YakshithK/K-Logic/Screenshots/Screenshot 2026-03-21 152913.png

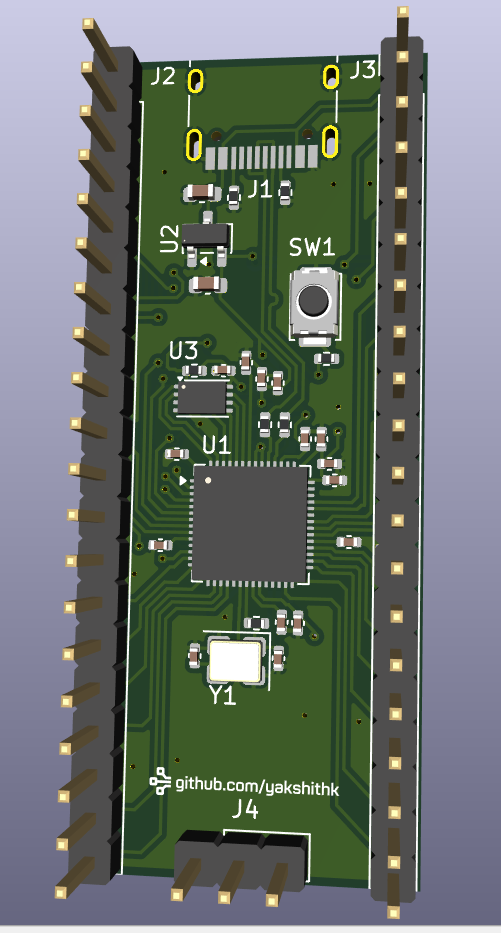
Screenshots/Screenshot 2026-03-21 152913.png
