YakshithK/K-Logic/Screenshots/Screenshot 2026-03-10 000626.png

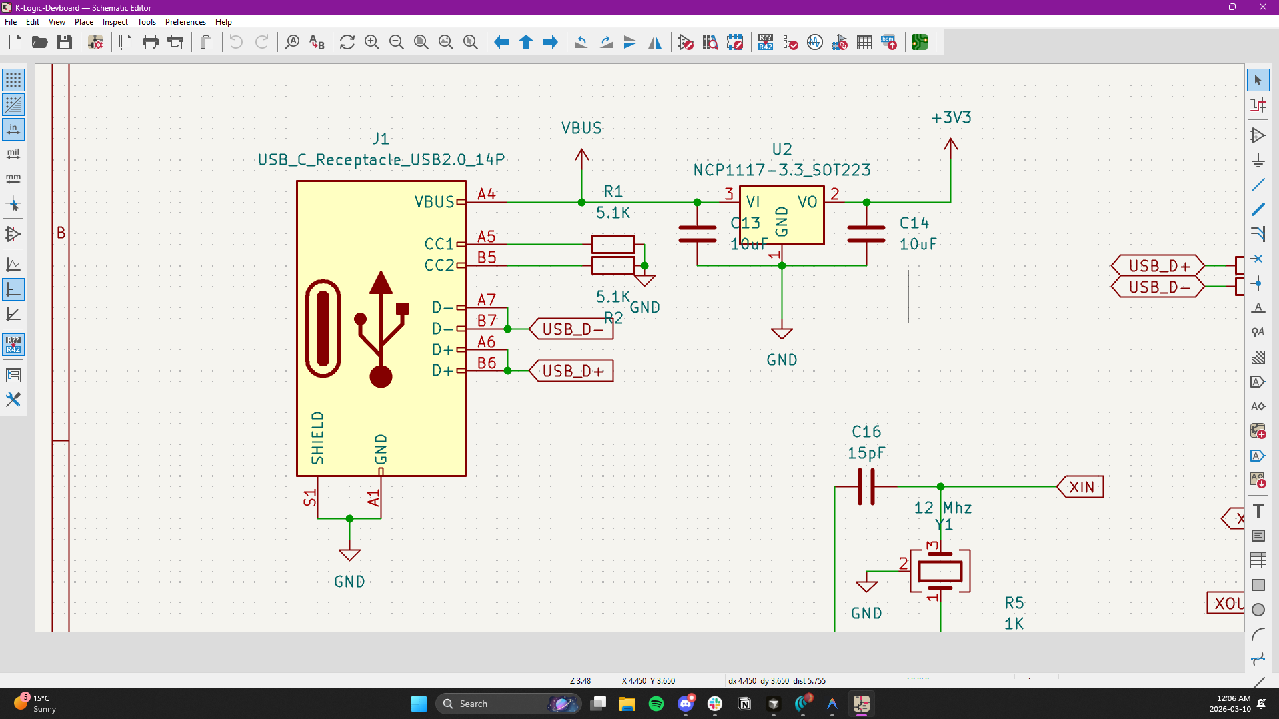
Screenshots/Screenshot 2026-03-10 000626.png
