YakshithK/K-Logic/Screenshots/Screenshot 2026-03-10 092232.png

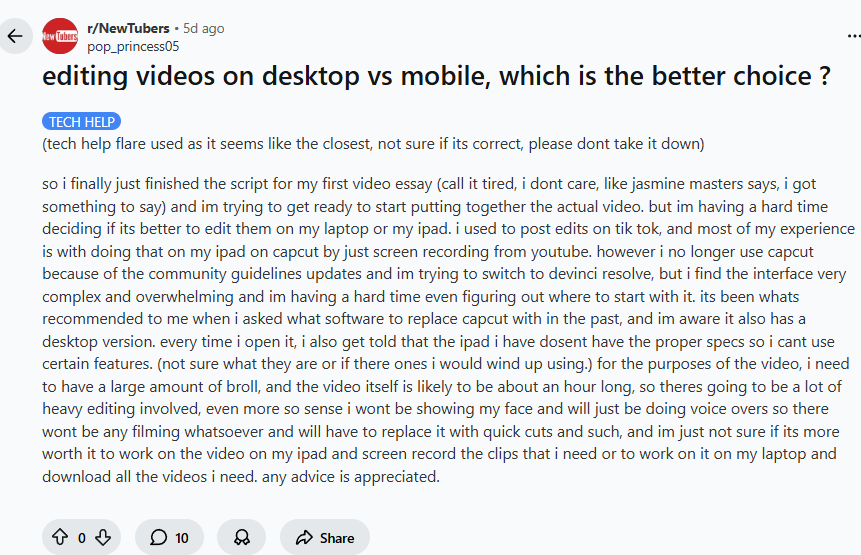
Screenshots/Screenshot 2026-03-10 092232.png
