YakshithK/K-Logic/Screenshots/Screenshot 2026-03-10 194304.png

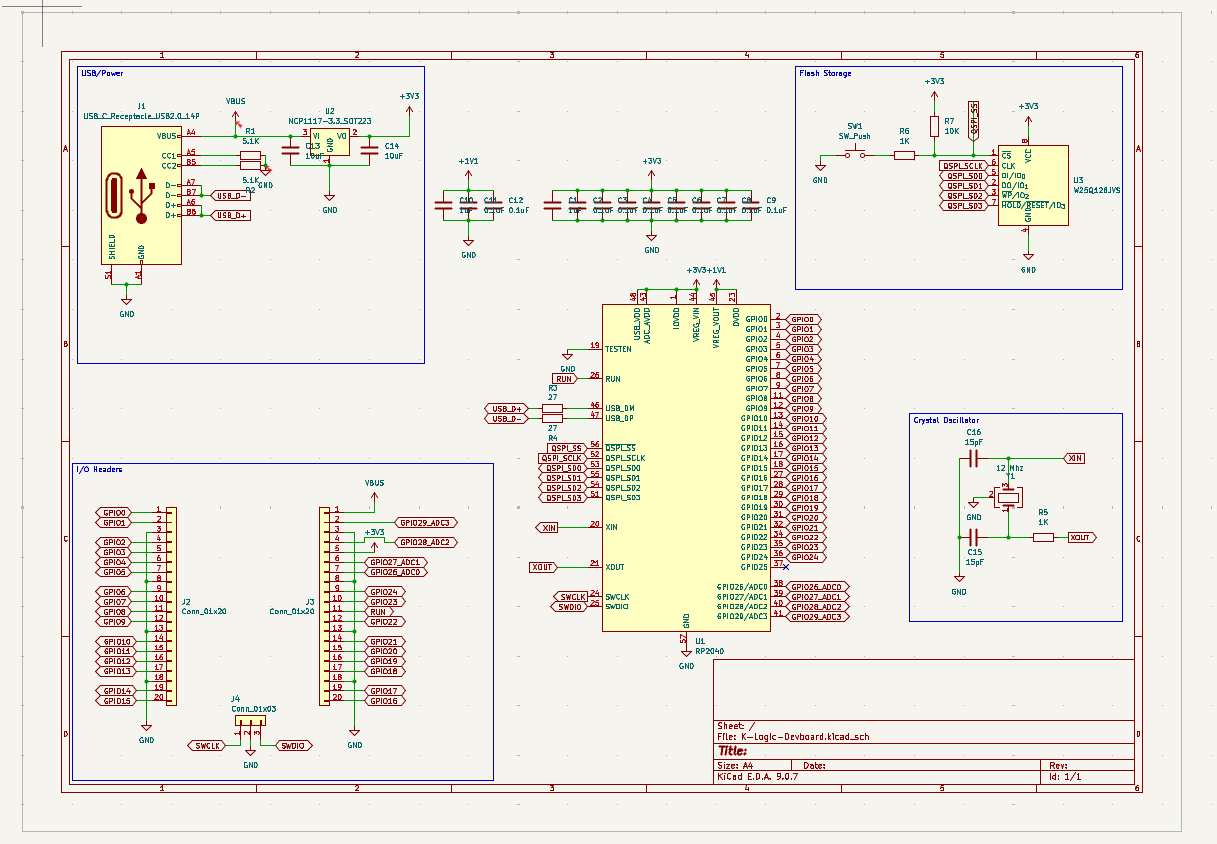
Screenshots/Screenshot 2026-03-10 194304.png
