YakshithK/K-Logic/Screenshots/Screenshot 2026-03-10 195755.png

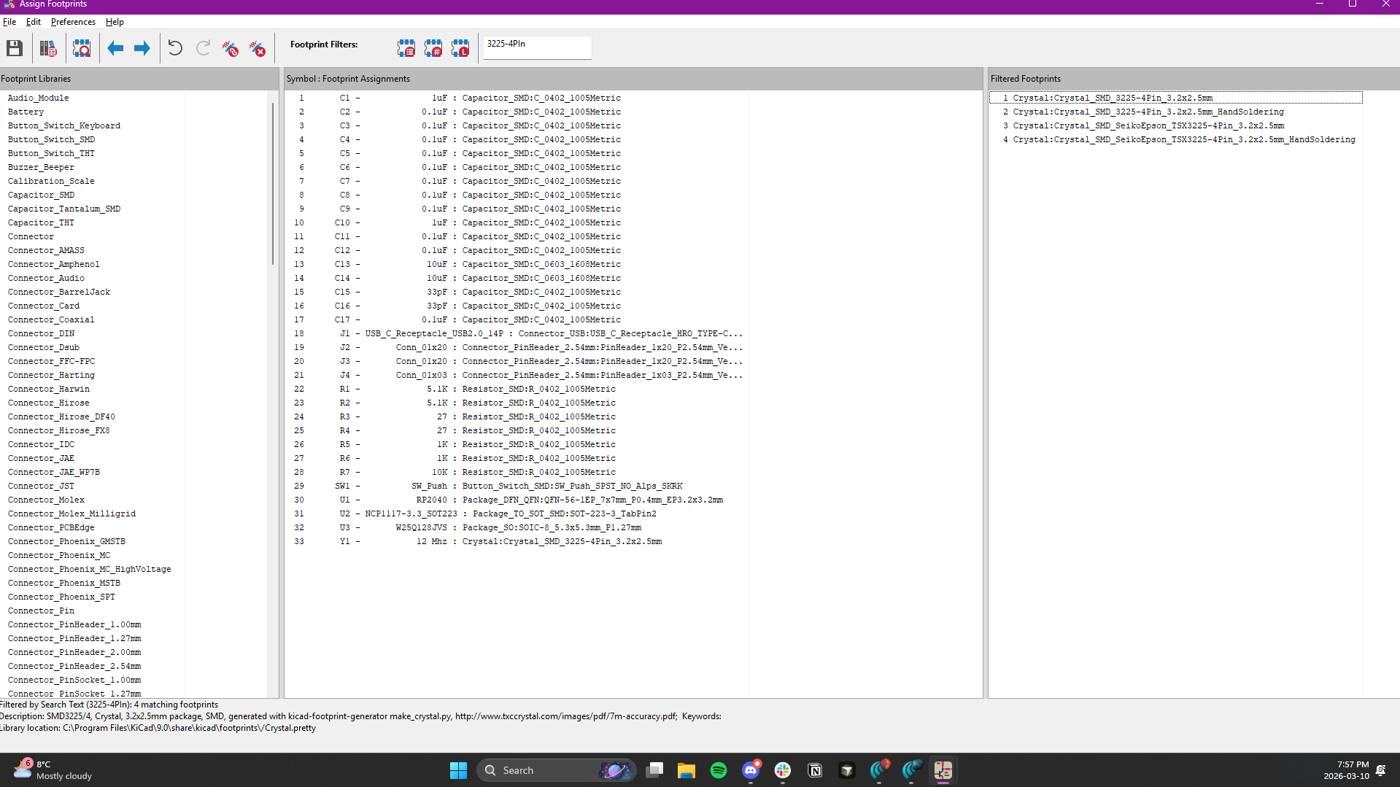
Screenshots/Screenshot 2026-03-10 195755.png
