YakshithK/K-Logic/Screenshots/Screenshot 2026-03-11 165531.png

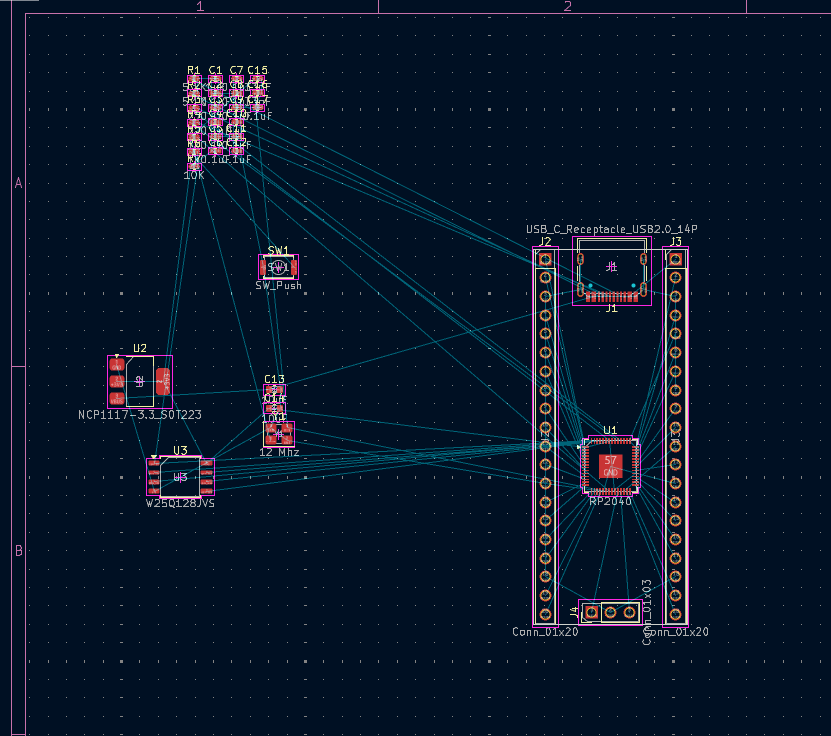
Screenshots/Screenshot 2026-03-11 165531.png
