YakshithK/K-Logic/Screenshots/Screenshot 2026-03-14 103205.png

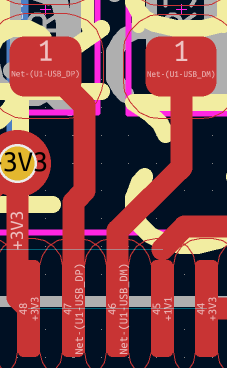
Screenshots/Screenshot 2026-03-14 103205.png
