YakshithK/K-Logic/Screenshots/Screenshot 2026-03-14 105847.png

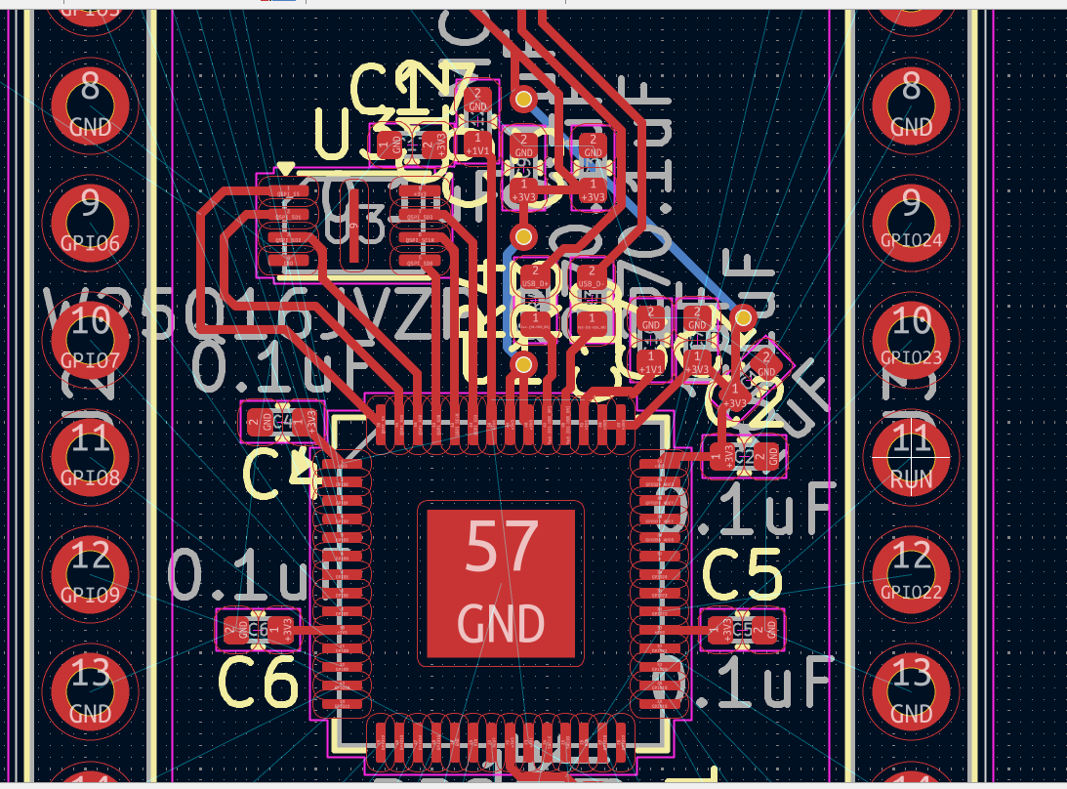
Screenshots/Screenshot 2026-03-14 105847.png
