YakshithK/K-Logic/Screenshots/Screenshot 2026-03-14 121532.png

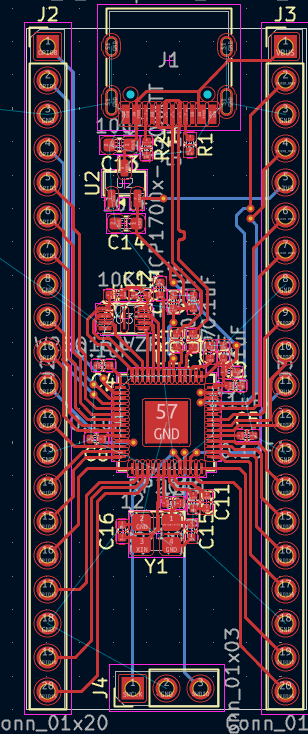
Screenshots/Screenshot 2026-03-14 121532.png
