YakshithK/K-Logic/Screenshots/Screenshot 2026-03-14 193433.png

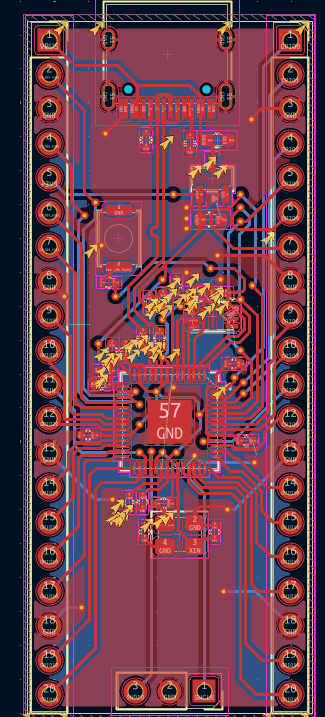
Screenshots/Screenshot 2026-03-14 193433.png
