YakshithK/K-Logic/Screenshots/Screenshot 2026-03-14 193438.png

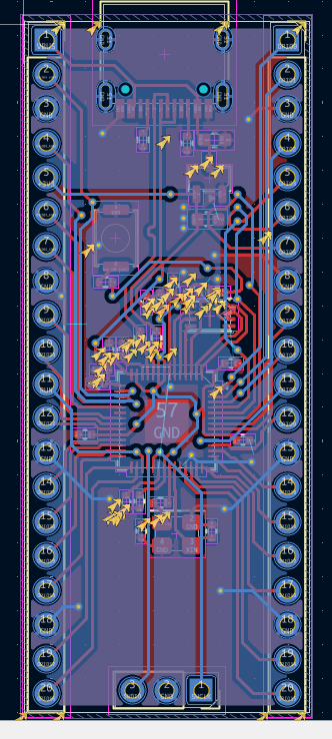
Screenshots/Screenshot 2026-03-14 193438.png
