YakshithK/K-Logic/Screenshots/Screenshot 2026-03-16 190729.png

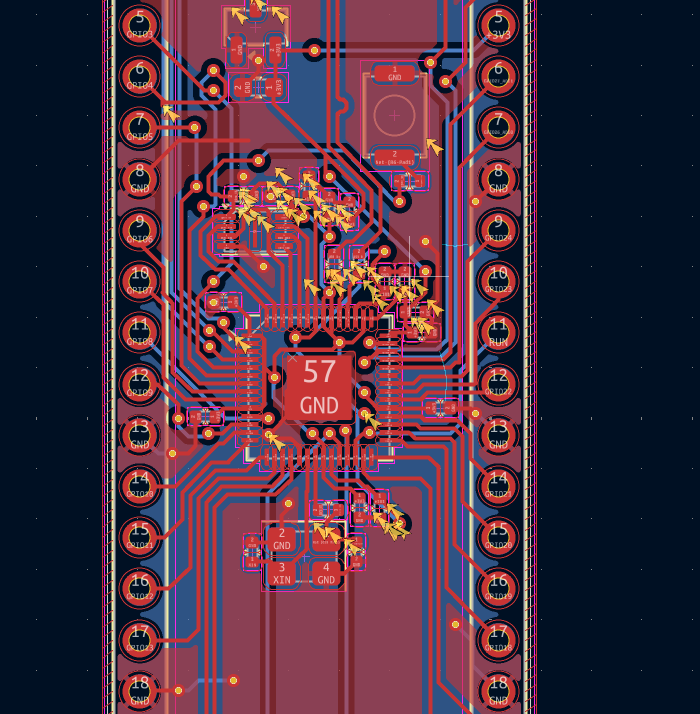
Screenshots/Screenshot 2026-03-16 190729.png
