YakshithK/K-Logic/Screenshots/Screenshot 2026-03-21 152852.png

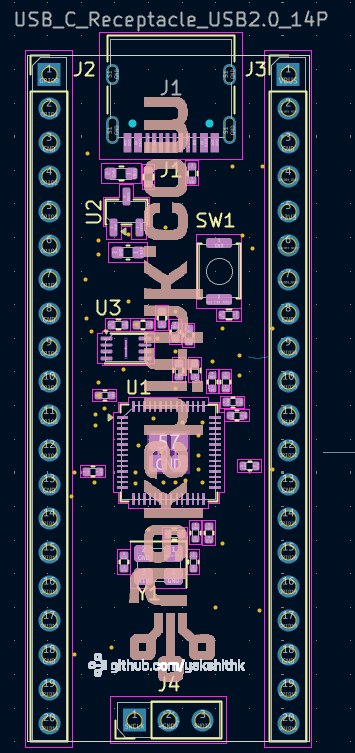
Screenshots/Screenshot 2026-03-21 152852.png
